lufixSch/sound-laser/docs/src/assets/pictures/circuit/amp_bode.png

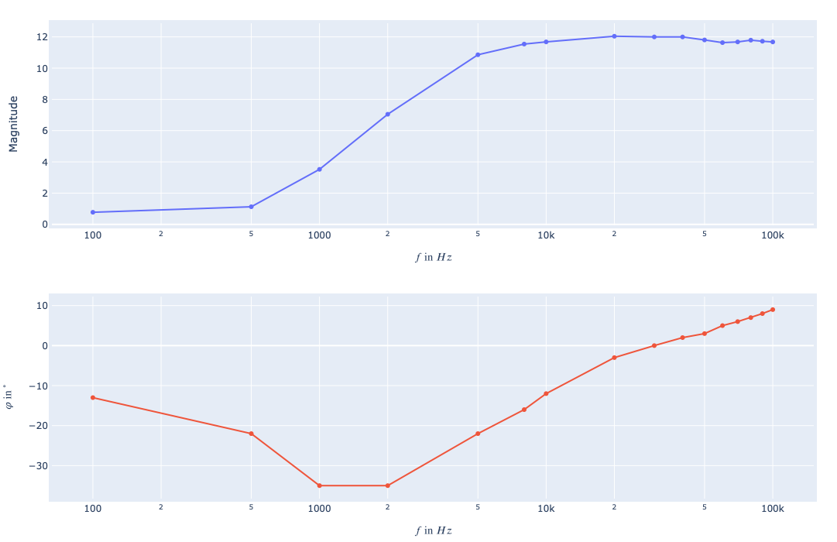
docs/src/assets/pictures/circuit/amp_bode.png
