lufixSch/sound-laser/docs/src/assets/pictures/circuit/amp_bode_small.png

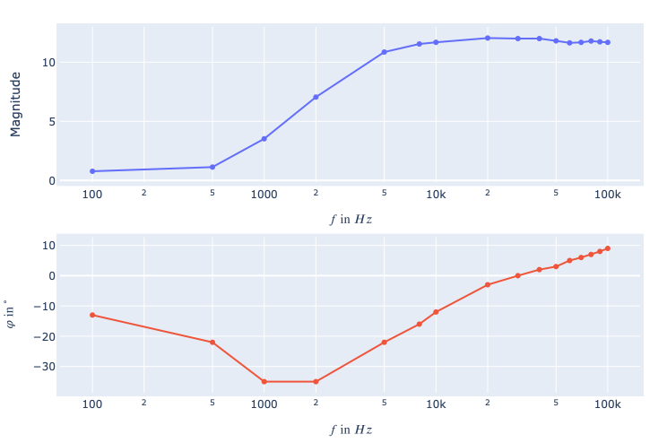
docs/src/assets/pictures/circuit/amp_bode_small.png
