lufixSch/sound-laser/docs/src/assets/pictures/software/control_interface.png

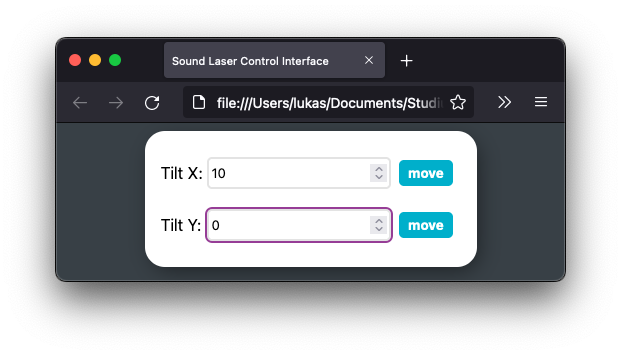
docs/src/assets/pictures/software/control_interface.png
