lufixSch/sound-laser/docs/src/assets/pictures/software/spi_enable_1.png

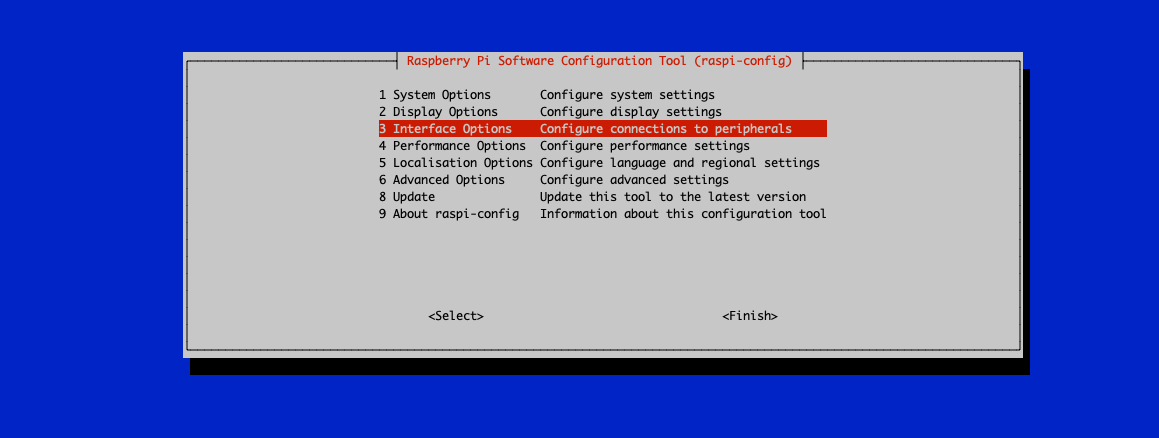
docs/src/assets/pictures/software/spi_enable_1.png
