lufixSch/sound-laser/docs/src/assets/pictures/software/spi_enable_3.png

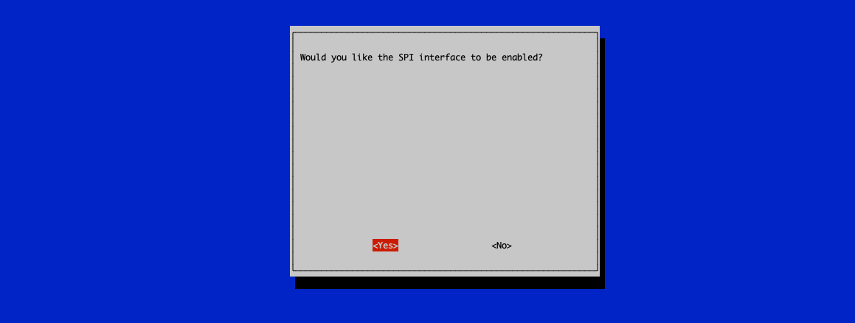
docs/src/assets/pictures/software/spi_enable_3.png
