lufixSch/sound-laser/hardware/verification/dac/2022-07-20_1_152030 (2).png

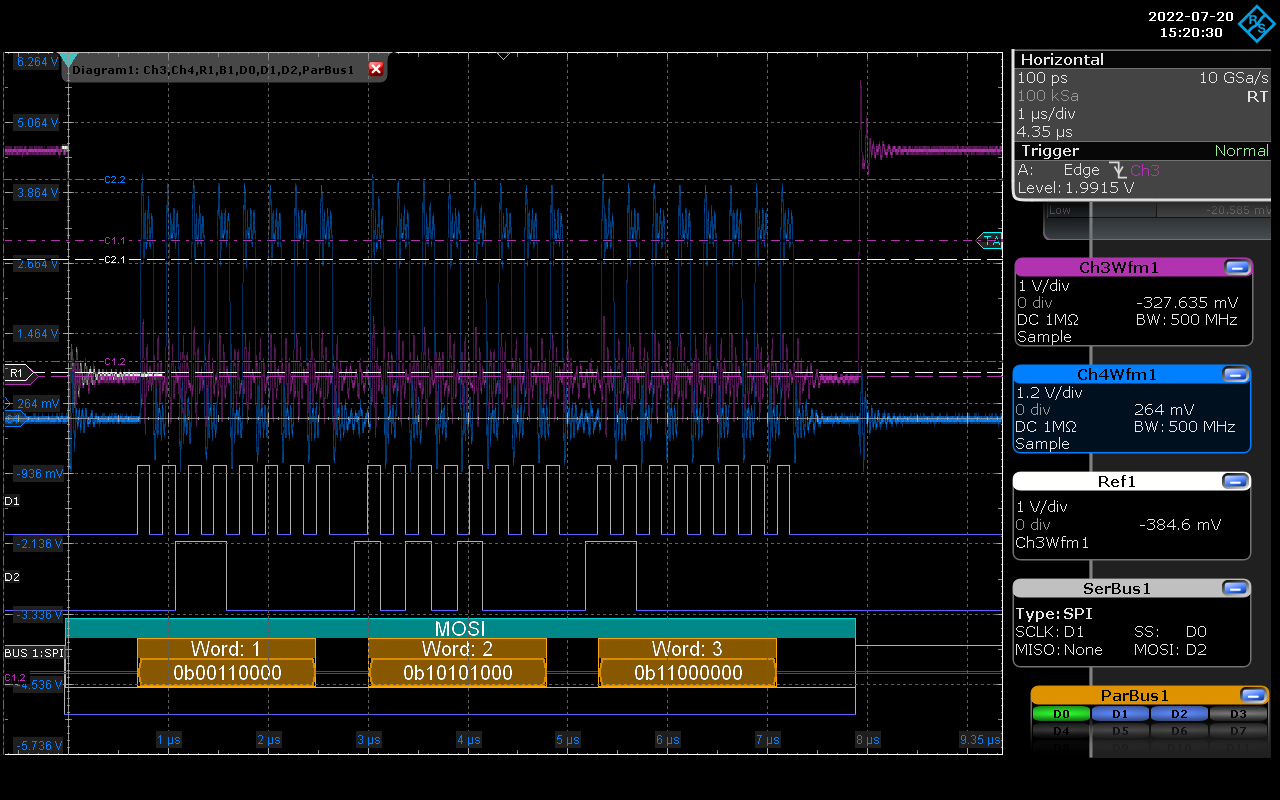
hardware/verification/dac/2022-07-20_1_152030 (2).png
