lufixSch/sound-laser/docs/src/assets/pictures/fh-logo.pdf

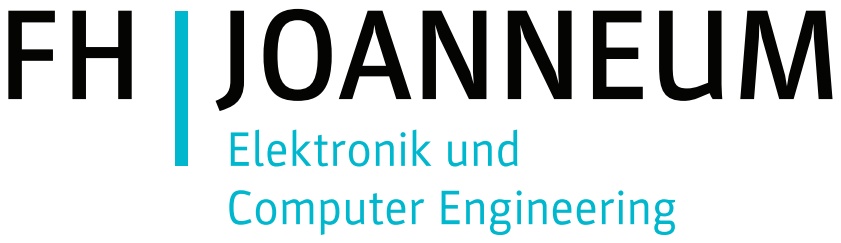
[picture p65: page 1]
