lufixSch/sound-laser/docs/src/assets/pictures/logo_FHJ_ECE_white-eps-converted-to.pdf

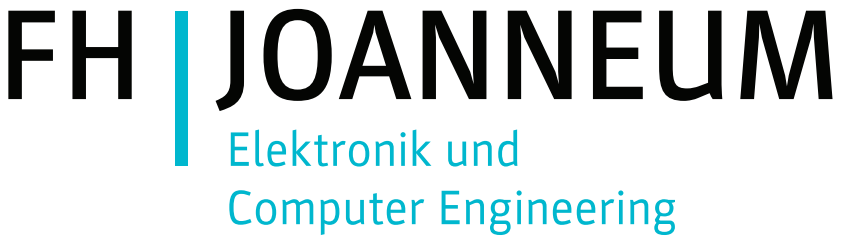
[picture p66: page 1]
