lufixSch/sound-laser/docs/src/assets/pictures/circuit/amp_stability.pdf

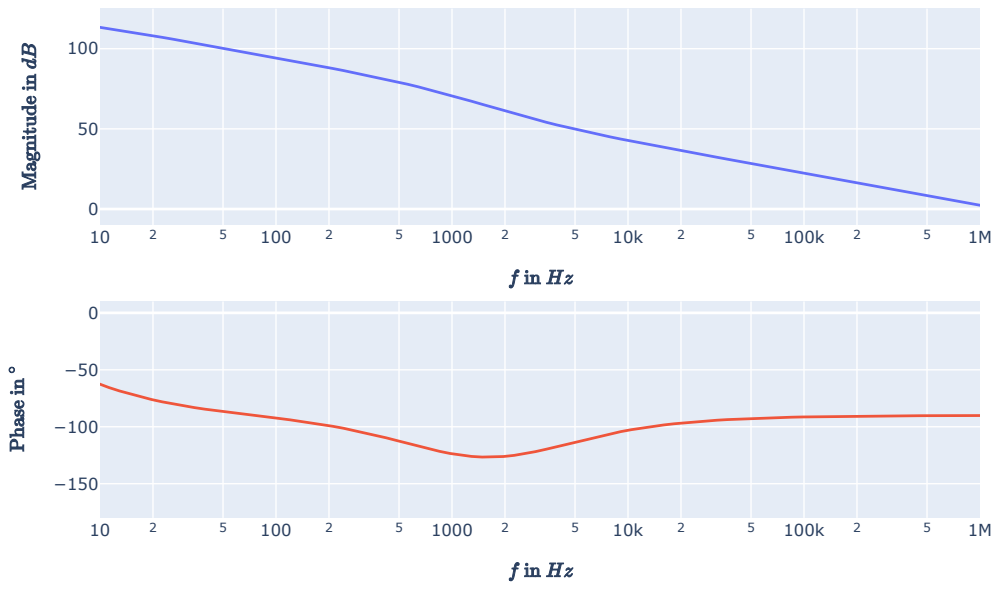
[picture p67: page 1]
