lufixSch/sound-laser/hardware/pcb/speaker/simulations/amplifier_sim.asc

C1: cap; 80n
C2: cap; 100n
C3: cap; 100n
C4: cap; 2.4p
R1: res; 10k
R2: res; 10k
R3: res; 16k
R4: res; 16k
U1: AD823
V1: voltage; 24
V2: signal; SINE(2.5 2.5 40k)
Named nets: 0, Vcc, sig
.tran 10m
